organisciak/cube-light/docs/wled-backup/settings-sync.png

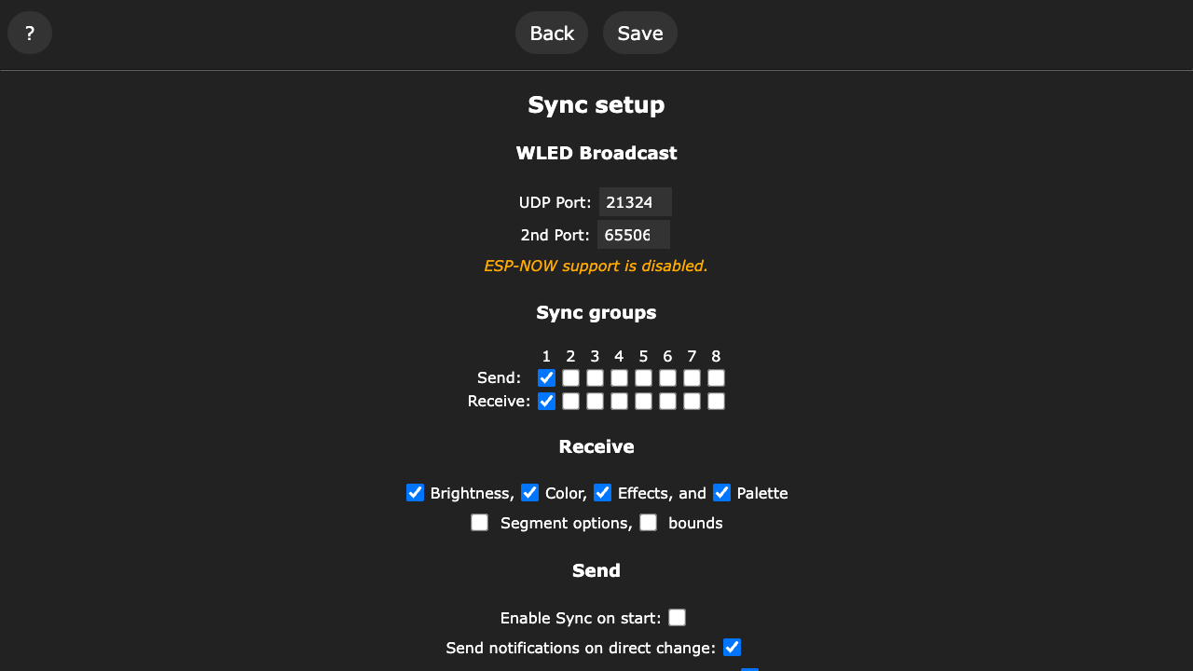
docs/wled-backup/settings-sync.png
